hannessenonerCTM/SVC_Model/LTSpice_simulation.asc

C1: cap; 100n
C3: cap; 82µ
C4: cap; 100n; ic=0
C5: cap; 10n
C6: cap; 82µ
C7: cap; 10n
C8: cap; 100n; ic=0
C9: cap; 10n
C10: cap; 82µ
D1: diode; RRD20TJ10S
D2: diode; RRD20TJ10S
D3: diode; RRD20TJ10S
D4: diode; RRD20TJ10S
D5: diode; RRD20TJ10S
D6: diode; RRD20TJ10S
D7: diode; RRD20TJ10S
D8: diode; RRD20TJ10S
D9: diode; RRD20TJ10S
D10: diode; RRD20TJ10S
D11: diode; RRD20TJ10S
D12: diode; RRD20TJ10S
D13: zener; KDZLV150
D14: zener; KDZLV150
D15: zener; KDZLV150
D16: zener; KDZLV150
D17: zener; KDZLV150
D18: zener; KDZLV150
D19: zener; KDZLV150
D20: zener; KDZLV150
D21: zener; KDZLV150
D22: zener; KDZLV150
D23: zener; KDZLV150
D24: zener; KDZLV150
L1: ind; 50m; ic=0
L2: ind; 50m; ic=0
L3: ind; 50m; ic=0
M1: nmos; STW11NM80
M2: nmos; STW11NM80
M3: nmos; STW11NM80
Q1: pnp; 2N2907
Q2: pnp; 2N2907
Q3: pnp; 2N2907
R1: res; 10k
R2: res; 1k
R3: res; 100k
R4: res; 1k
R5: res; 56
R6: res; 100
R7: res; 100
R8: res; 47
R9: res; 10k
R10: res; 1k
R11: res; 100k
R12: res; 1k
R13: res; 100
R14: res; 56
R15: res; 100
R16: res; 47
R17: res; 10k
R18: res; 1k
R19: res; 100k
R20: res; 1k
R21: res; 56
R22: res; 100
R23: res; 47
R24: res; 100
R25: res; 0.1
R26: res; 0.1
R27: res; 0.1
U1: MOC3020
U2: Littelfuse_TRIAC
U3: NE555
U4: MOC206
U5: NE555
U6: MOC206
U7: Littelfuse_TRIAC
U8: MOC3020
U9: NE555
U10: MOC206
U11: Littelfuse_TRIAC
U12: MOC3020
V1: voltage; SINE(0 155 50 0 0 240)
V2: voltage; 5
V3: voltage; 5; Rser=1
V4: voltage; 2.1
V5: voltage; SINE(0 155 50 0 0 120)
V6: voltage; SINE(0 155 50 0 0 0)
V7: voltage; 5; Rser=1
V8: voltage; 5; Rser=1
Named nets: 0, 5V, L1, L2, L3, Vref
DBF1510U
.tran 0 0.14 0.04
2 - 3.15V
DBF1510U
DBF1510U
QK008LH4 (same device, isolated tab)
